HandHeldLegend/Latte-HW/3D/STEP/Acrylic/PRO_SEWN.step

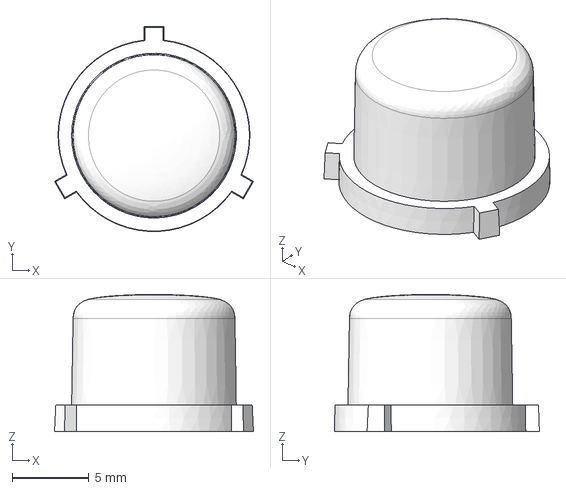
[picture p12: CAD file, 2026-04-08]
3D/STEP/Acrylic/PRO_SEWN.step
13.0 x 13.3 x 8.95 mm
