HandHeldLegend/Latte-HW/3D/STL/TRIGGER.stl

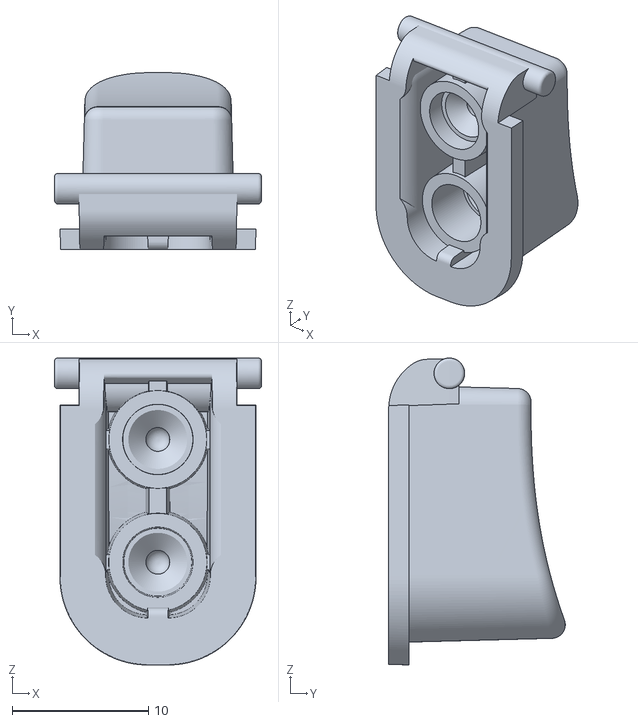
[picture p13: CAD file, 2026-04-08]
3D/STL/TRIGGER.stl
15.2 x 12.9 x 22.5
