HandHeldLegend/Latte-HW/3D/STEP/Acrylic/PRO_PLAYERLIGHTS.step

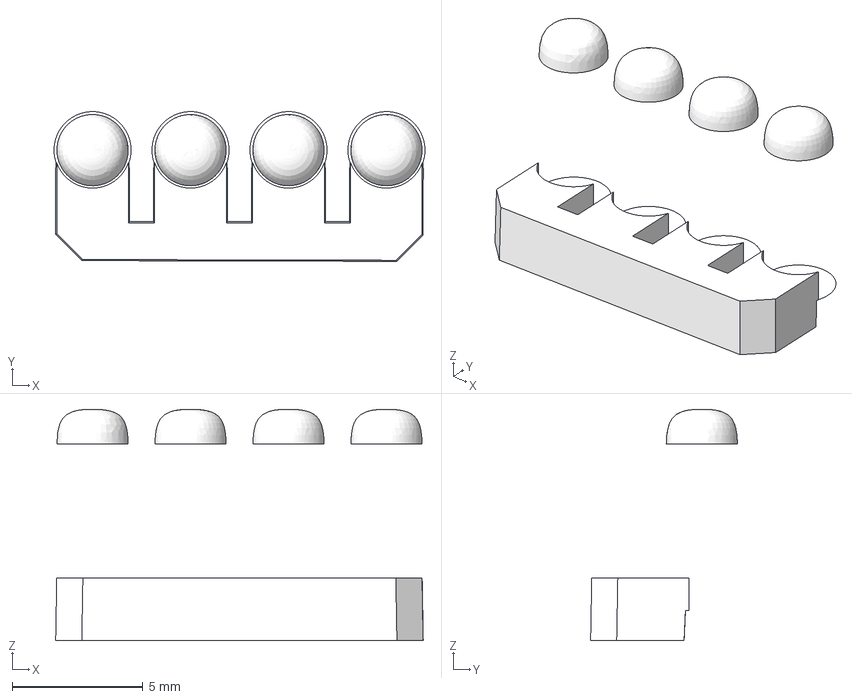
[picture p14: CAD file, 2026-04-08]
3D/STEP/Acrylic/PRO_PLAYERLIGHTS.step
14.2 x 5.73 x 8.86 mm
