HandHeldLegend/Latte-HW/3D/STL/PLAYERLIGHTS.stl

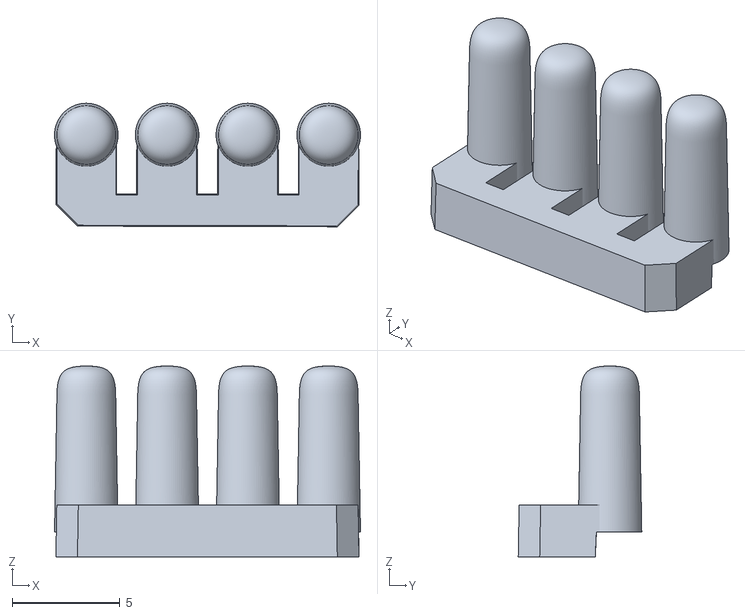
[picture p15: CAD file, 2025-11-12]
3D/STL/PLAYERLIGHTS.stl
14.2 x 5.73 x 8.86
